aterry35/pi_klydo_clock/designs/paper-cut/preview.png

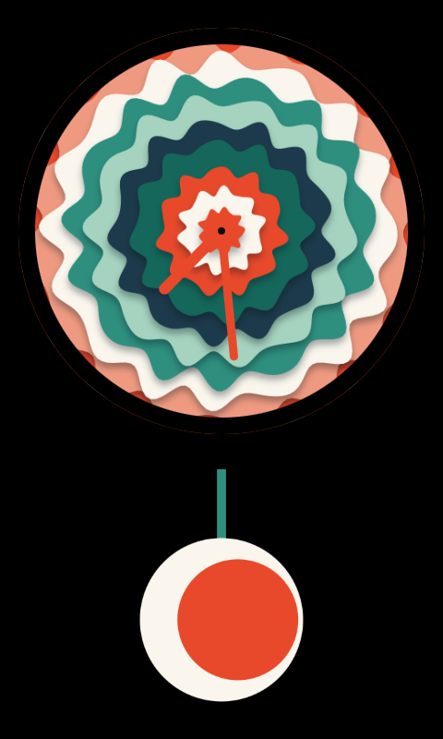
designs/paper-cut/preview.png
