aterry35/pi_klydo_clock/docs/images/enclosure/clock_back.png

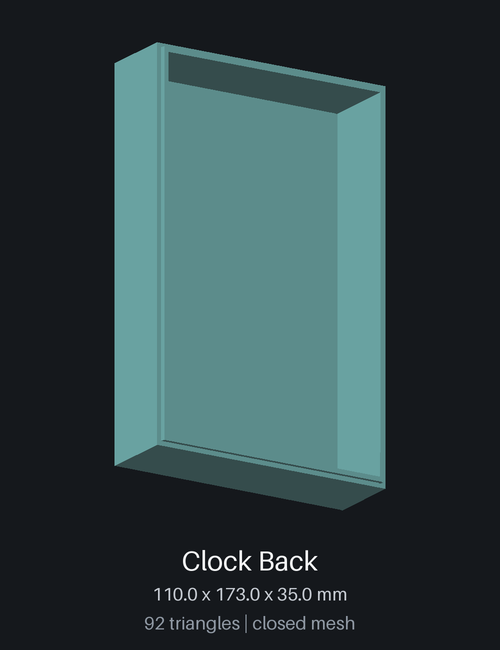
docs/images/enclosure/clock_back.png
