aterry35/pi_klydo_clock/docs/images/enclosure/clock_face.png

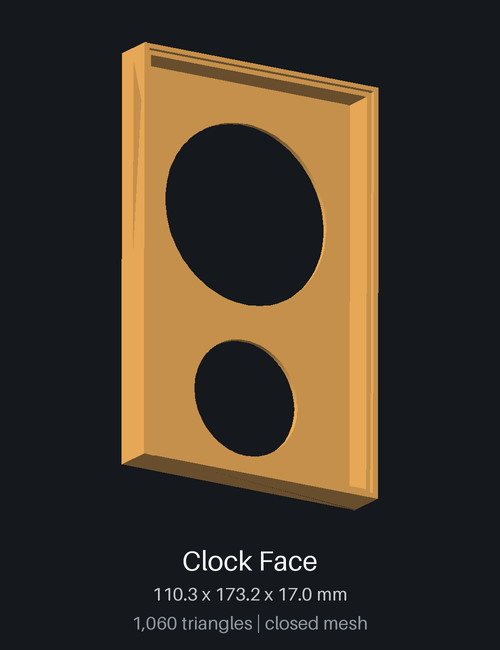
docs/images/enclosure/clock_face.png
