aterry35/pi_klydo_clock/docs/images/enclosure/clock_frame.png

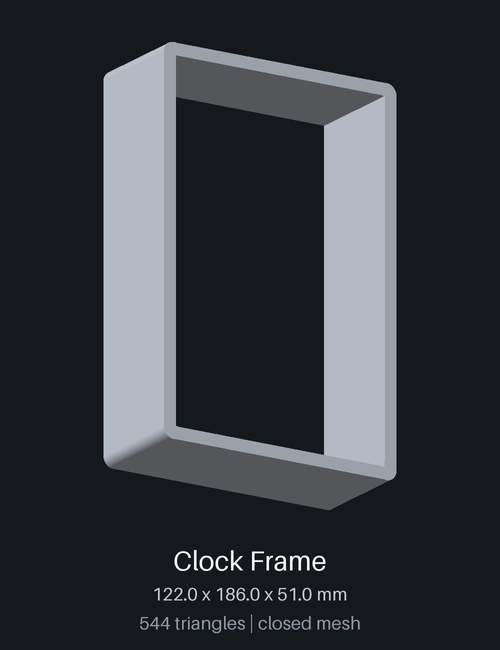
docs/images/enclosure/clock_frame.png
